mneha05/envirobridge-kicad/EnviroBridge.sch

## KiCad design EnviroBridge.sch (2026-09-24)

Schematic: EnviroBridge.sch

Parts:
C1, C2: 100n
C3: 4.7u
J1: HOST; PinHeader_1x04_P2.54mm_Vertical
R1, R2: 4.7k
U1, U2: BME280; LGA-8_2.5x2.5mm_P0.65mm

Notes on the sheet:
U1 SDO strap -> GND (0x76)
U2 SDO strap -> 3V3 (0x77)
J1: GND / 3V3 / SDA / SCL
